Netwxx/improved_8_wire_cable_tester/Wiring Diagram/Schematic.kicad_sch

## KiCad design Wiring Diagram/Schematic.kicad_sch (2026-06-06)

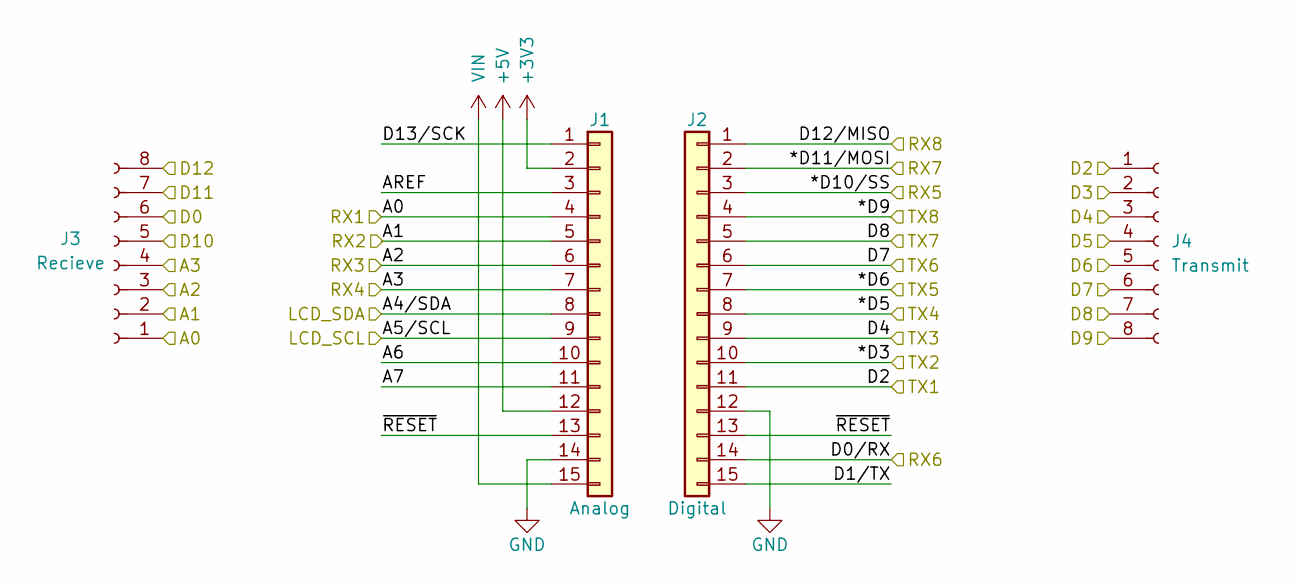
[picture p2: schematic Schematic.kicad_sch]

Parts:
J1: Analog; PinHeader_1x15_P2.54mm_Vertical
J2: Digital; PinHeader_1x15_P2.54mm_Vertical
J3: Recieve
J4: Transmit

Connections:
+3V3: J1.2
+5V: J1.12
A0: J1.4, J3.1
A1: J1.5, J3.2
A2: J1.6, J3.3
A3: J1.7, J3.4
A4/SDA: J1.8
A5/SCL: J1.9
A6: J1.10
A7: J1.11
AREF: J1.3
D0: J3.6
D0/RX: J2.14
D1/TX: J2.15
D2: J2.11, J4.1
D3: J2.10, J4.2
D4: J2.9, J4.3
D5: J2.8, J4.4
D6: J2.7, J4.5
D7: J2.6, J4.6
D8: J2.5, J4.7
D9: J2.4, J4.8
D10: J3.5
D11: J3.7
D12: J3.8
D12/MISO: J2.1
D13/SCK: J1.1
GND: J1.14, J2.12
VIN: J1.15
d10/ss: J2.3
d11/mosi: J2.2
~RESET: J1.13, J2.13
